briantdavis/EAS_BBB_DataAcquisition/source/eas_main.h

//
// EagleAeroSport
//
// B.Davis
//
//////////////////
// this is the structure which contains the data which is SHARED not replicated
// between the parallel threads of execution.
/*
typedef struct shared_vars {

  bool         gDone;
  bool         gAccelEnabled;
  bool         gPressEnabled;
  bool         gTempEnabled;
  unsigned int iLoopPause;
  uint8_t      gNextUniqueID;

} shared_vars_t;
*/
